SloBloLabs/TahomaRemote/App/StreamBuffer.cpp

#include "StreamBuffer.h"
#include <cstring>

void streamBufferInit(StreamBuffer_t* sb) {
    streamBufferFlush(sb);
    sb->size = sizeof(sb->buffer);
}

void streamBufferFlush(StreamBuffer_t* sb) {
    sb->head = 0;
    sb->tail = 0;
    sb->count = 0;
    memset(sb->buffer, 0, sb->size);
}

void streamBufferPush(StreamBuffer_t* sb, char c) {
    // If buffer is full, discard oldest data (overwrite tail)
    if(sb->count >= sb->size) {
        sb->tail = (sb->tail + 1) % sb->size;
    } else {
        sb->count++;
    }
    
    sb->buffer[sb->head] = c;
    sb->head = (sb->head + 1) % sb->size;
}

char streamBufferPop(StreamBuffer_t* sb) {
    if(sb->count == 0) {
        return 0;
    }
    
    char c = sb->buffer[sb->tail];
    sb->tail = (sb->tail + 1) % sb->size;
    sb->count--;
    return c;
}

// Creates a temporary linear view of the ring buffer. tempBuffer must be at
// least STREAM_BUFFER_CAPACITY + 1 bytes (sb->count can never exceed sb->size,
// and sb->size is set to STREAM_BUFFER_CAPACITY in streamBufferInit()).
static void streamBufferLinearize(StreamBuffer_t* sb, char* tempBuffer) {
    uint16_t pos = sb->tail;
    for(uint16_t i = 0; i < sb->count; i++) {
        tempBuffer[i] = sb->buffer[pos];
        pos = (pos + 1) % sb->size;
    }
    tempBuffer[sb->count] = 0;
}

bool streamBufferContains(StreamBuffer_t* sb, const char* token) {
    if(!token || sb->count == 0) {
        return false;
    }
    
    size_t tokenLen = strlen(token);
    if(tokenLen > sb->count) {
        return false;
    }
    
    char tempBuffer[STREAM_BUFFER_CAPACITY + 1];
    streamBufferLinearize(sb, tempBuffer);
    
    // Search for token
    return strstr(tempBuffer, token) != NULL;
}

void streamBufferContainsTokens(StreamBuffer_t* sb, const char* tokenA, bool* foundA, const char* tokenB, bool* foundB) {
    *foundA = false;
    *foundB = false;
    if(sb->count == 0) {
        return;
    }
    
    char tempBuffer[STREAM_BUFFER_CAPACITY + 1];
    streamBufferLinearize(sb, tempBuffer);
    
    if(tokenA && strlen(tokenA) <= sb->count) {
        *foundA = strstr(tempBuffer, tokenA) != NULL;
    }
    if(tokenB && strlen(tokenB) <= sb->count) {
        *foundB = strstr(tempBuffer, tokenB) != NULL;
    }
}

uint16_t streamBufferGetCount(StreamBuffer_t* sb) {
    return sb->count;
}
